fcte-pi1/2026_1_PI1_Grupo01_Hilmer/hw/diagrama_blocos.jpg

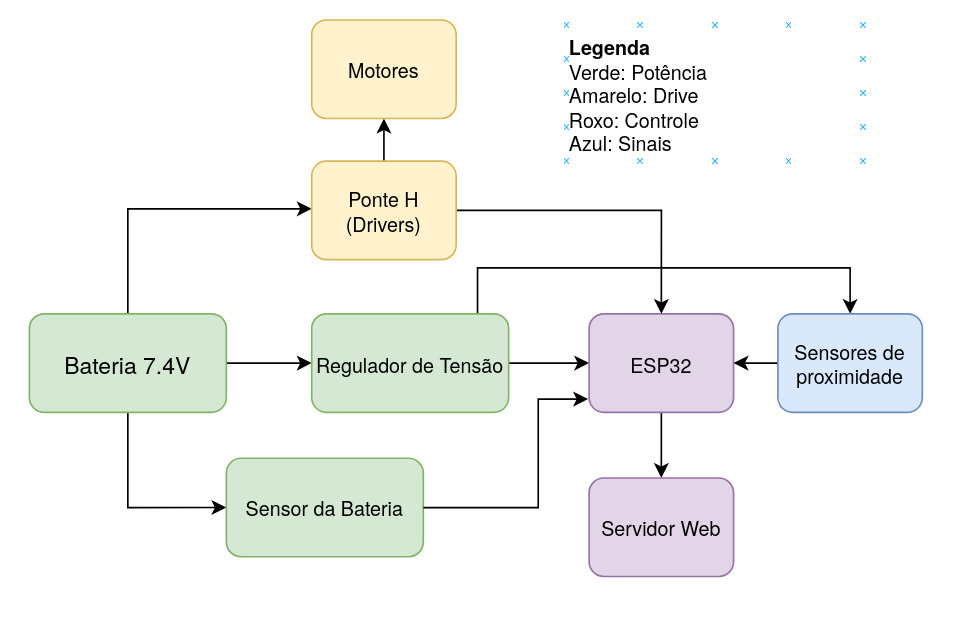
hw/diagrama_blocos.jpg
