fcte-pi1/2026_1_PI1_Grupo01_Hilmer/hw/img/13.jpeg

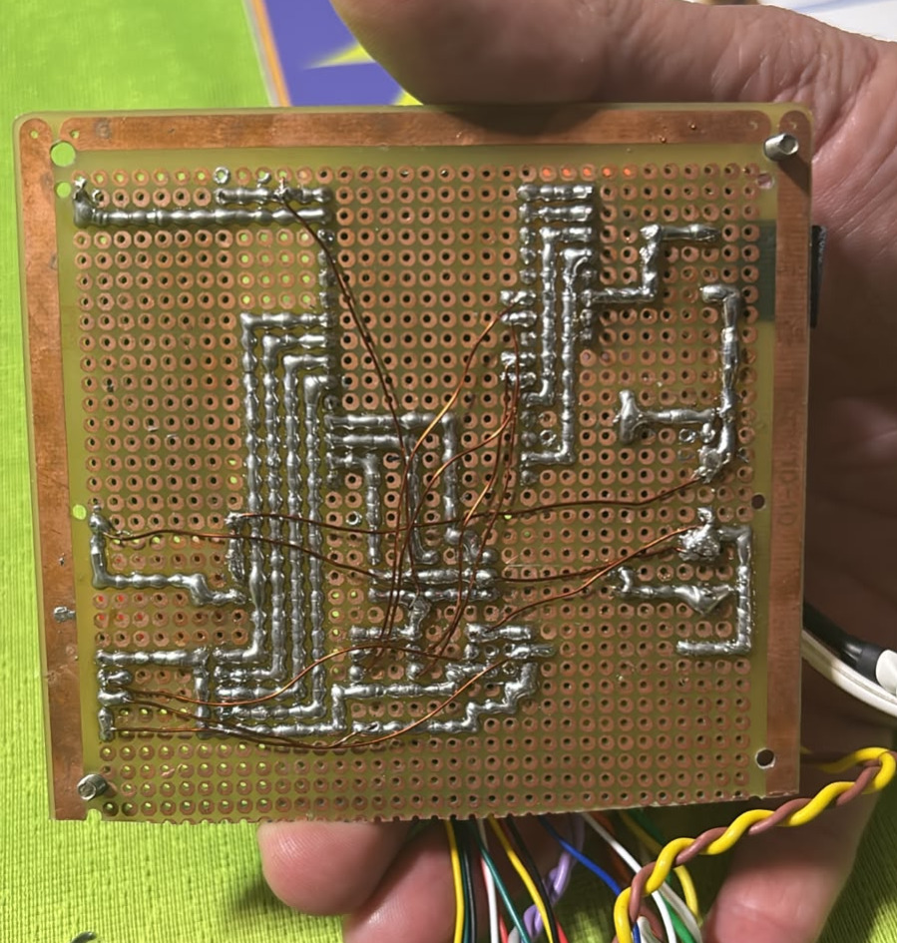
hw/img/13.jpeg
