fcte-pi1/2026_1_PI1_Grupo01_Hilmer/mec/Docs/explodida.jpg

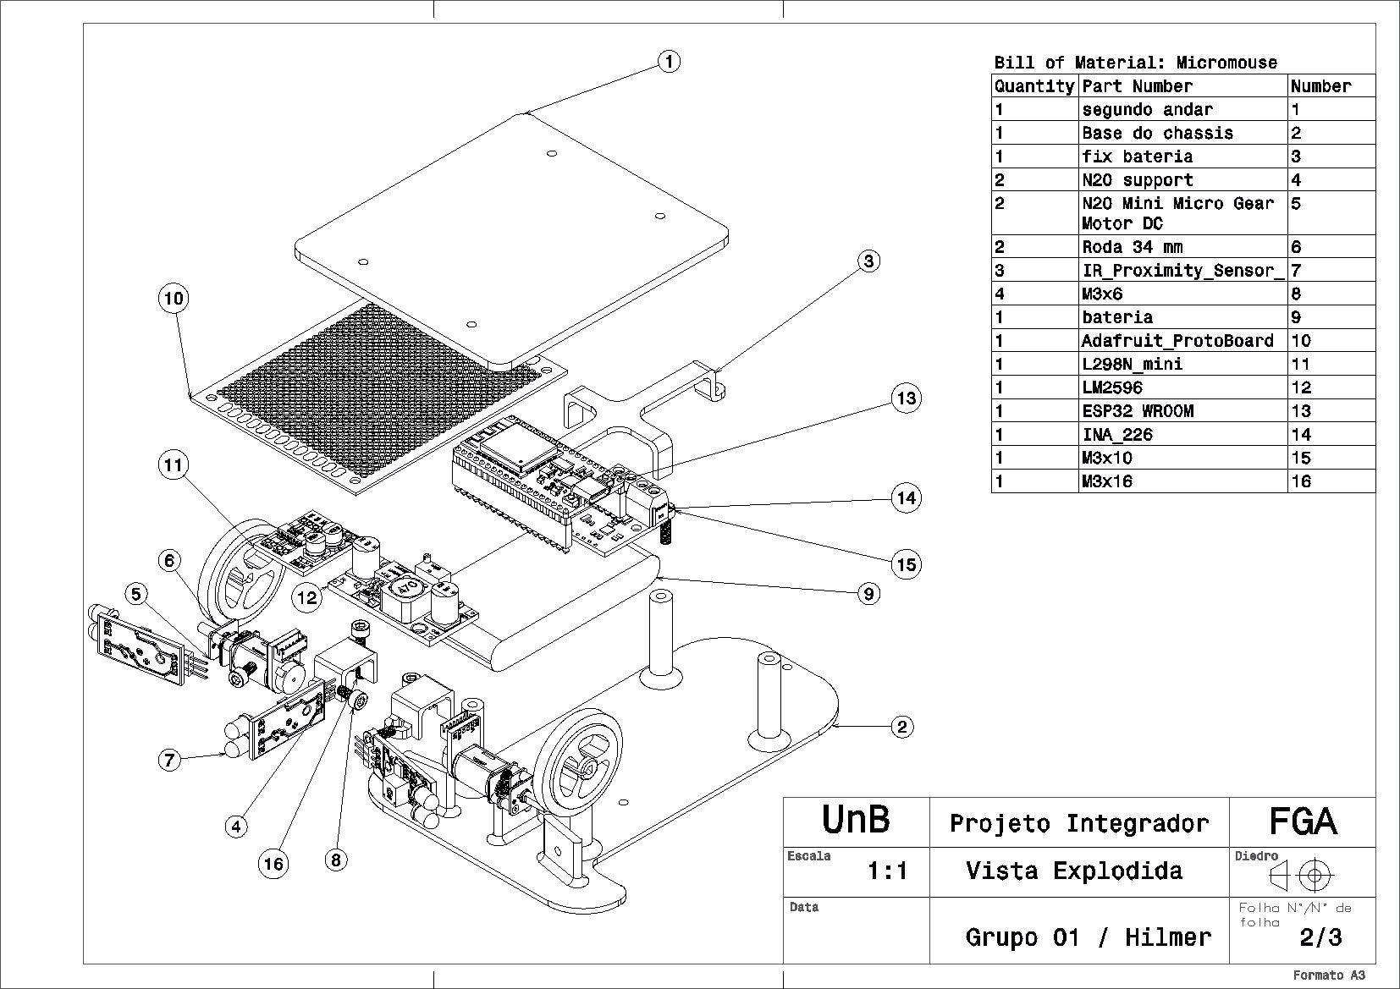
mec/Docs/explodida.jpg
