fcte-pi1/2026_1_PI1_Grupo01_Hilmer/mec/Docs/vistas.jpg

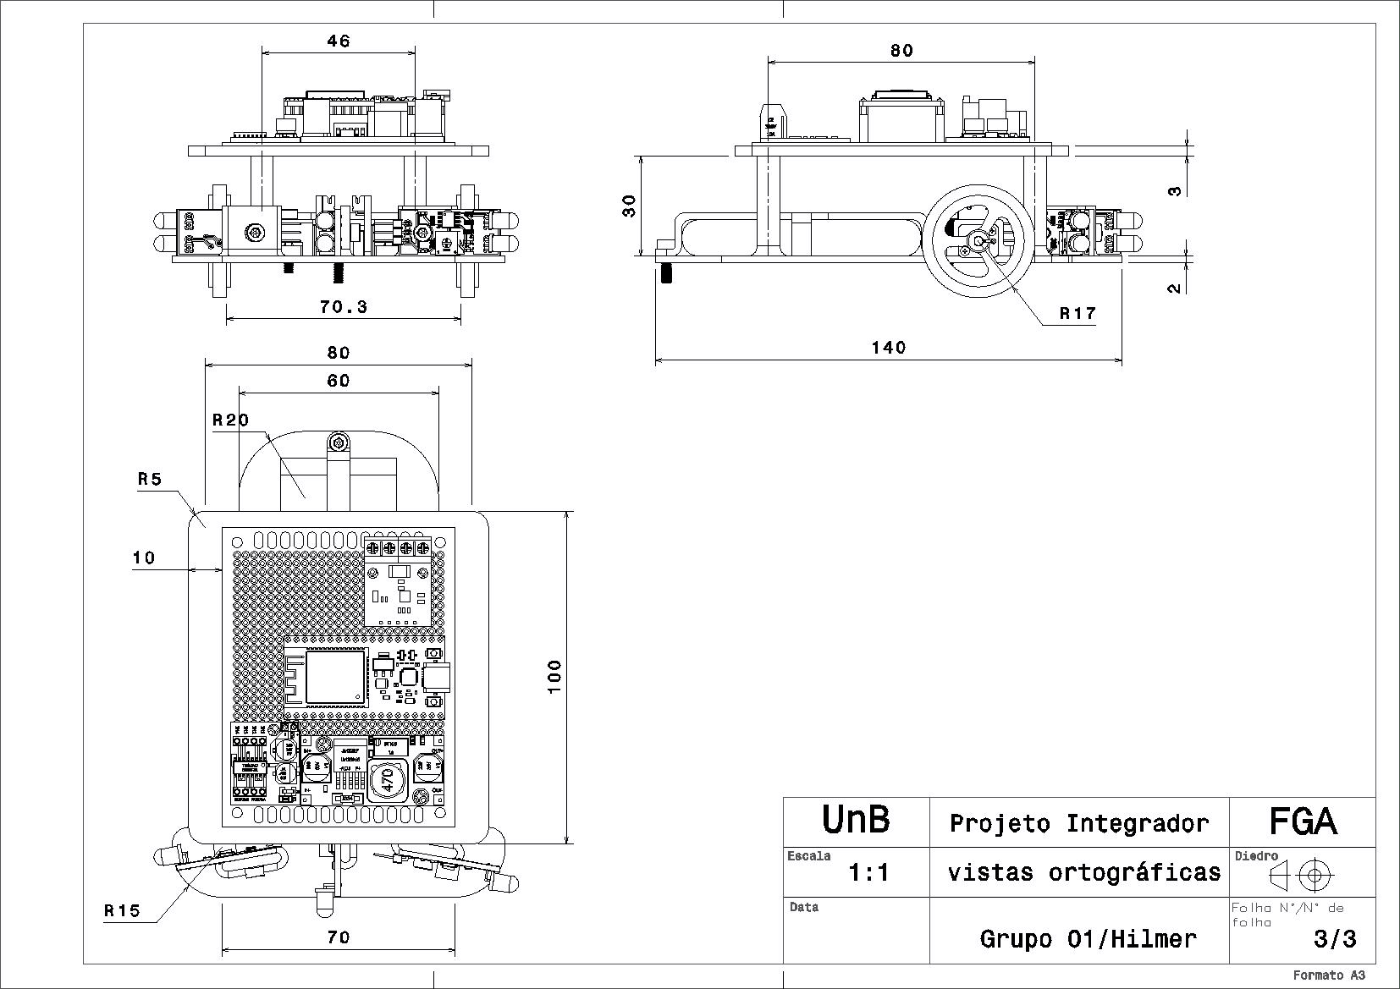
mec/Docs/vistas.jpg
