fcte-pi1/2026_1_PI1_Grupo01_Hilmer/src/firmware/src/main.cpp

#include <Arduino.h>
#include <Wire.h>
#include <SparkFun_APDS9960.h>
#include <ArduinoJson.h> // Adicionado: Necessário para a sintaxe do objeto 'doc' funcionar

// Definindo os pinos I2C padrão para a ESP32-C3
#define I2C_SDA 21
#define I2C_SCL 22

SparkFun_APDS9960 apds = SparkFun_APDS9960();

// Adicionado: Objeto global de telemetria para permitir o uso de doc["..."]
StaticJsonDocument<200> doc;

uint16_t luzAmbienteBase = 0;

void setup() {
  Serial.begin(115200);
  Wire.begin(I2C_SDA, I2C_SCL);

  Serial.println("Inicializando Sensor RGB APDS-9960...");

  // Inicializa o sensor
  if (apds.init()) {
    Serial.println("APDS-9960 inicializado com sucesso!");
  } else {
    Serial.println("Falha ao inicializar o sensor. Verifique as conexões I2C.");
  }

  // Habilita a leitura de cores e luz ambiente
  if (apds.enableLightSensor(false)) {
    Serial.println("Leitor de cores ativado!");
  } else {
    Serial.println("Erro ao ativar leitor de cores.");
  }

  // Adicionado: Inicializa a variável de telemetria pedida na mensagem ("N" = Não completado)
  doc["desafioCumprido"] = "N";

  // Salva o valor da luz da sala assim que o robô liga para sabermos o "zero" do ambiente
  delay(500);
  apds.readAmbientLight(luzAmbienteBase);
}

void loop() {
  uint16_t r = 0, g = 0, b = 0, c = 0;

  // Realiza a leitura dos canais de cor
  if (apds.readRedLight(r) && apds.readGreenLight(g) && apds.readBlueLight(b) && apds.readAmbientLight(c)) {
    // Desconta o excesso de luz da sala para o valor lido ser real e não sofrer interferência externa
    if (c > luzAmbienteBase) {
      uint16_t excessoLuz = c - luzAmbienteBase;
      r = (r > excessoLuz) ? (r - excessoLuz) : 0;
    }
    
    Serial.printf("Cores - R: %d | G: %d | B: %d | Ambiente: %d\n", r, g, b, c);

    // LÓGICA DE FIM DE LABIRINTO
    // Exemplo: Se o centro do labirinto for uma fita vermelha no chão
    if (r > 200 && g < 100 && b < 100) {
      Serial.println("🎯 FIM DO LABIRINTO DETECTADO! Acionando freios...");
      
      // Transforma o comentário em linha de código ativa para atualizar a telemetria
      doc["desafioCumprido"] = "S";
    }
  }

  delay(200); // 5Hz de frequência de leitura para não sobrecarregar a rotina principal
}
