fcte-pi1/2026_1_PI1_Grupo01_Hilmer/src/firmware/sensor_bateria/micromouse/src/main.cpp

#ifndef PIO_UNIT_TESTING

#include <Arduino.h>

#include "battery.h"
#include "telemetry.h"

void setup()
{
    Serial.begin(115200);

    delay(1000);

    initBatteryMonitor();
}

void loop()
{
    printTelemetry();

    delay(1000);
}

#endif
