fcte-pi1/2026_1_PI1_Grupo01_Hilmer/src/firmware/sensor_bateria/micromouse/include/battery.h

#ifndef BATTERY_H
#define BATTERY_H

void initBatteryMonitor();

float readVoltage();

float readCurrent();

float readPower();

bool lowBattery(float voltage);

bool veryLowBattery(float voltage);

bool criticalBattery(float voltage);

float batteryPercentage(float voltage);

#endif
