fcte-pi1/2026_1_PI1_Grupo01_Hilmer/src/firmware/sensor_bateria/micromouse/src/telemetry.cpp

#ifndef PIO_UNIT_TESTING

#include <Arduino.h>

#include "battery.h"
#include "telemetry.h"

void printTelemetry()
{
    float voltage = readVoltage();

    float current = readCurrent();

    float power = readPower();

    Serial.println("====================");

    Serial.print("Voltage: ");
    Serial.print(voltage);
    Serial.println(" V");

    Serial.print("Current: ");
    Serial.print(current);
    Serial.println(" A");

    Serial.print("Power: ");
    Serial.print(power);
    Serial.println(" W");

    if (criticalBattery(voltage))
    {
        Serial.println("CRITICAL BATTERY");
    }
    else if (veryLowBattery(voltage))
    {
        Serial.println("VERY LOW BATTERY");
    }
    else if (lowBattery(voltage))
    {
        Serial.println("LOW BATTERY");
    }
    else
    {
        Serial.println("BATTERY OK");
    }
}

float percentage =
    batteryPercentage(voltage);

Serial.print("Battery: ");
Serial.print(percentage);
Serial.println("%");

#endif
